Theo-Marshall/SHIFTR-Hardware/include/UUIDs.h

#ifndef UUIDS_H
#define UUIDS_H

#define ZWIFT_CUSTOM_SERVICE_UUID "00000001-19CA-4651-86E5-FA29DCDD09D1"
#define ZWIFT_ASYNC_CHARACTERISTIC_UUID "00000002-19CA-4651-86E5-FA29DCDD09D1"
#define ZWIFT_SYNCRX_CHARACTERISTIC_UUID "00000003-19CA-4651-86E5-FA29DCDD09D1"
#define ZWIFT_SYNCTX_CHARACTERISTIC_UUID "00000004-19CA-4651-86E5-FA29DCDD09D1"

#define CYCLING_POWER_SERVICE_UUID "00001818-0000-1000-8000-00805f9b34fb"
#define CYCLING_POWER_MEASUREMENT_CHARACTERISTIC_UUID "00002a63-0000-1000-8000-00805f9b34fb"

#define CYCLING_SPEED_AND_CADENCE_SERVICE "00001816-0000-1000-8000-00805f9b34fb"
#define CYCLING_SPEED_AND_CADENCE_MEASUREMENT_CHARACTERISTIC "00002a5b-0000-1000-8000-00805f9b34fb"

#define TACX_FEC_PRIMARY_SERVICE_UUID "6e40fec1-b5a3-f393-e0a9-e50e24dcca9e"
#define TACX_FEC_READ_CHARACTERISTIC_UUID "6e40fec2-b5a3-f393-e0a9-e50e24dcca9e"
#define TACX_FEC_WRITE_CHARACTERISTIC_UUID "6e40fec3-b5a3-f393-e0a9-e50e24dcca9e"

#define FITNESS_MACHINE_SERVICE_UUID "00001826-0000-1000-8000-00805f9b34fb"
#define FITNESS_MACHINE_FEATURE_CHARACTERISTIC_UUID "00002acc-0000-1000-8000-00805f9b34fb"
#define INDOOR_BIKE_DATA_CHARACTERISTIC_UUID "00002ad2-0000-1000-8000-00805f9b34fb"
#define TRAINING_STATUS_CHARACTERISTIC_UUID "00002ad3-0000-1000-8000-00805f9b34fb"
#define FITNESS_MACHINE_CONTROL_POINT_CHARACTERISTIC_UUID "00002ad9-0000-1000-8000-00805f9b34fb"
#define FITNESS_MACHINE_STATUS_CHARACTERISTIC_UUID "00002ada-0000-1000-8000-00805f9b34fb"

#endif
