Theo-Marshall/SHIFTR-Hardware/include/ServiceManagerCallbacks.h

#ifndef SERVICEMANAGERCALLBACKS_H
#define SERVICEMANAGERCALLBACKS_H

#include <Service.h>

class ServiceManagerCallbacks {
 public:
  virtual ~ServiceManagerCallbacks() {}
  virtual void onServiceAdded(Service* service) {};
  virtual void onCharacteristicSubscriptionChanged(Characteristic* characteristic, bool removed) {};
};

#endif
