Theo-Marshall/SHIFTR-Hardware/include/BTClientCallbacks.h

#ifndef BTCLIENTCALLBACKS_H
#define BTCLIENTCALLBACKS_H

#include <NimBLEDevice.h>

class BTClientCallbacks : public NimBLEClientCallbacks {
  void onConnect(NimBLEClient* pClient);
  void onDisconnect(NimBLEClient* pClient, int reason);
  bool onConnParamsUpdateRequest(NimBLEClient* pClient, const ble_gap_upd_params* params);
};

#endif
